duckyb/urchin/gallery/case/iamDrakkir/cad-side-pcb.png

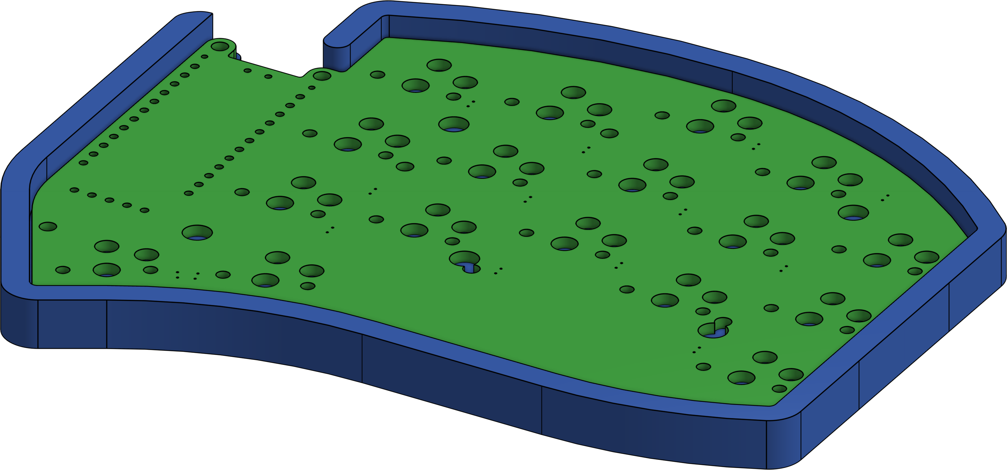
gallery/case/iamDrakkir/cad-side-pcb.png
