duckyb/urchin/gallery/main/main-bottom.png

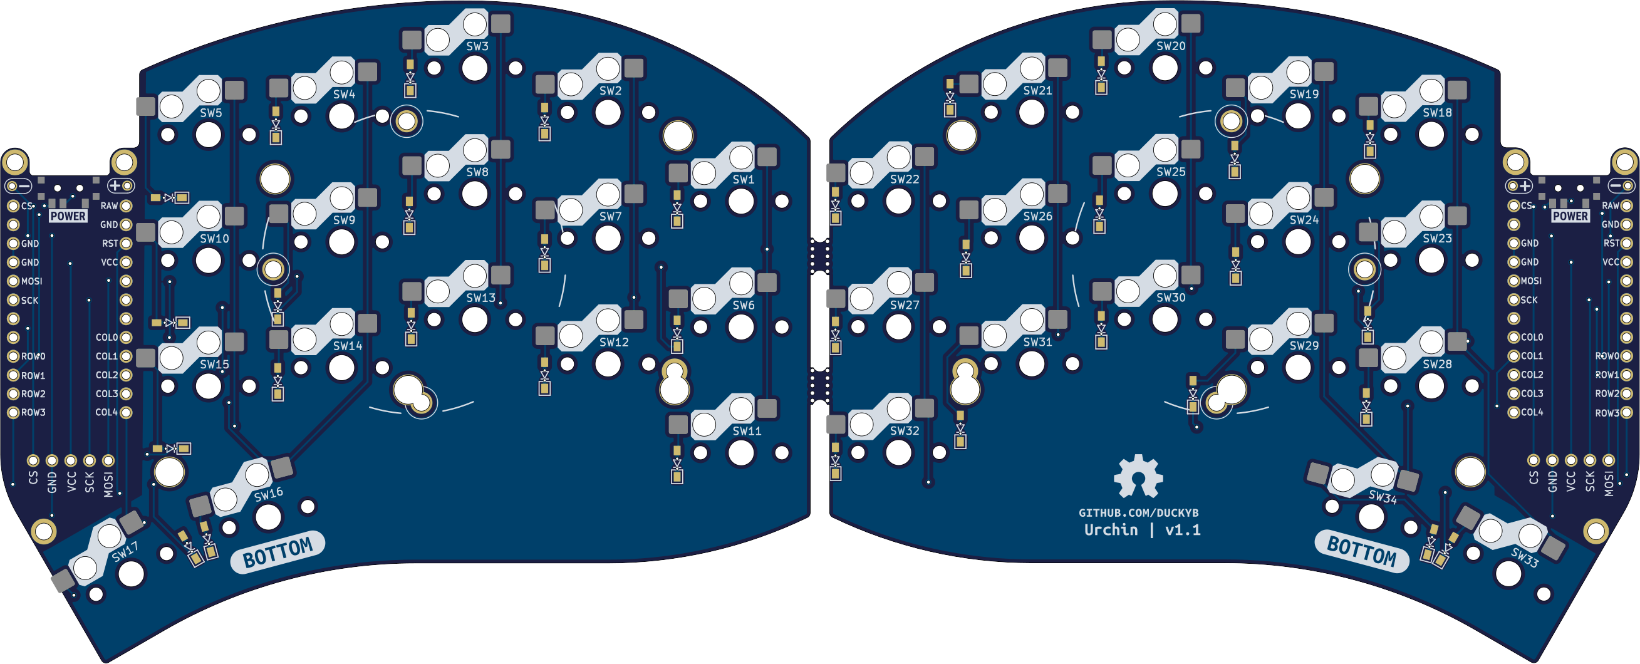
gallery/main/main-bottom.png
