duckyb/urchin/3d-prints/boxy-case-by-rayreside/urchin_boxy_top_right.stl

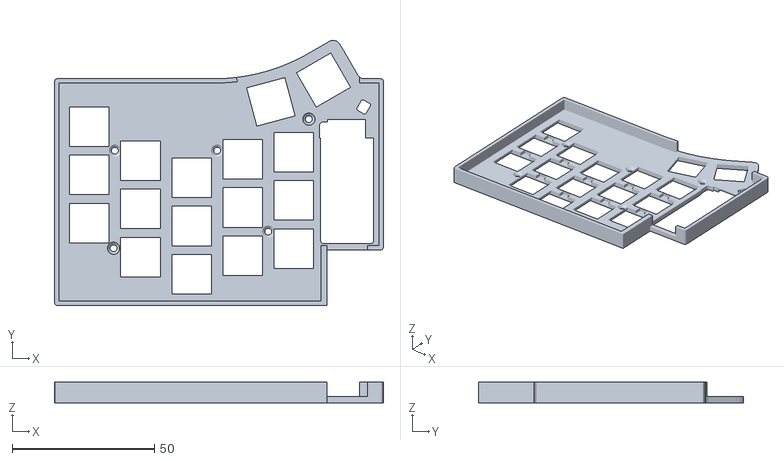
[picture p24: CAD file, 2026-08-28]
3d-prints/boxy-case-by-rayreside/urchin_boxy_top_right.stl
115.8 x 93.4 x 7.28
