duckyb/urchin/3d-prints/case-by-carrefino/urchin_case_right.stl

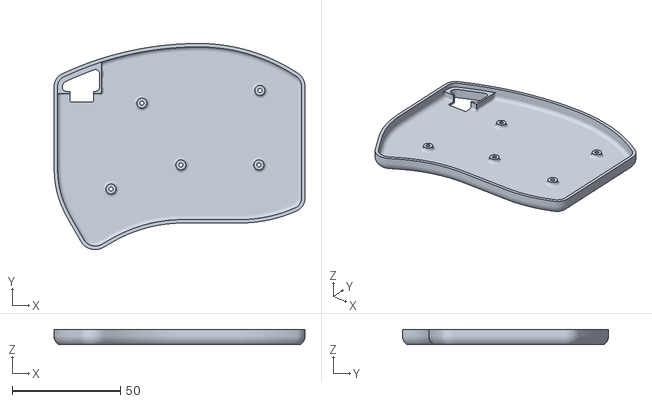
[picture p25: CAD file, 2024-06-18]
3d-prints/case-by-carrefino/urchin_case_right.stl
115.8 x 95.1 x 6.80
