duckyb/urchin/3d-prints/switch-plate/skeleton__plate.stl

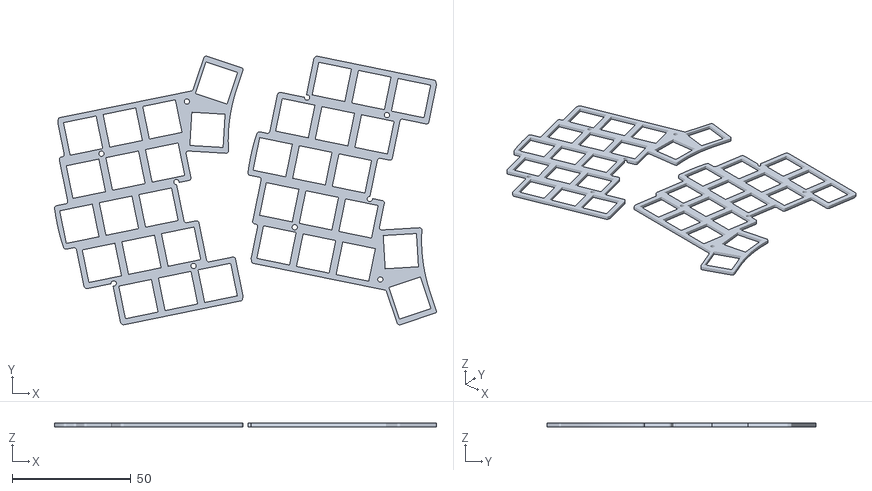
[picture p26: CAD file, 2024-11-27]
3d-prints/switch-plate/skeleton__plate.stl
160.6 x 113.0 x 1.60
