duckyb/urchin/3d-prints/boxy-case-by-rayreside/urchin_boxy_mountains_right.stl

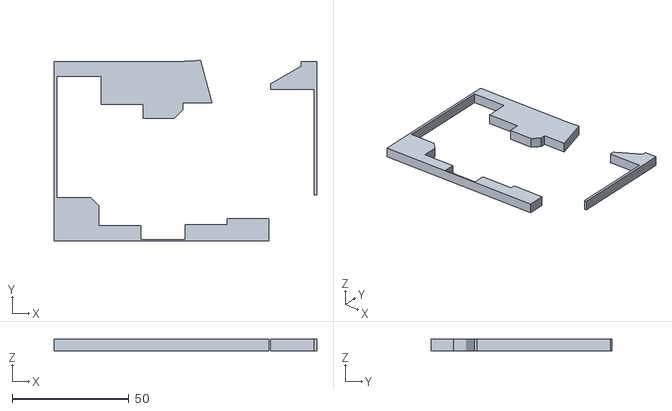
[picture p27: CAD file, 2026-08-28]
3d-prints/boxy-case-by-rayreside/urchin_boxy_mountains_right.stl
112.7 x 77.4 x 5.08
