duckyb/urchin/3d-prints/case-by-carrefino/Urchin Plate Case.step

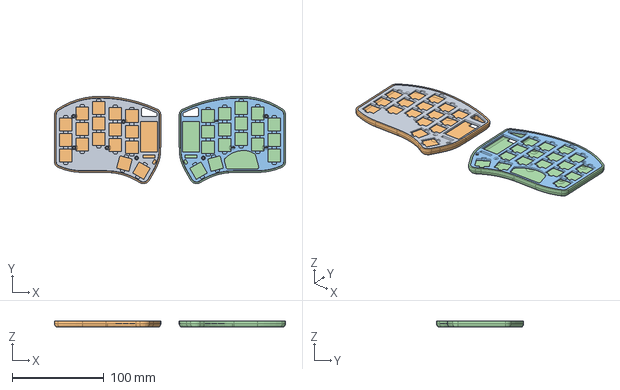
[picture p29: CAD file, 2024-06-18]
3d-prints/case-by-carrefino/Urchin Plate Case.step
251.7 x 95.1 x 6.80 mm
